MiikaRitokangas/SpedenSpelit/buttons.h

#ifndef BUTTONS_H
#define BUTTONS_H
#include <arduino.h>
#include <avr/io.h>
#include <avr/interrupt.h>

#define BUTTON0_PIN 2
#define BUTTON1_PIN 3
#define BUTTON2_PIN 4
#define BUTTON3_PIN 5
#define BUTTON4_PIN 6

const byte firstPin = 2; // First PinChangeInterrupt on D-bus
const byte lastPin =  5; // Last PinChangeInterrupt on D-bus

/* 
  initButtonsAndButtonInterrupts subroutine is called from Setup() function
  during the initialization of Speden Spelit. This function does the following:
  1) Initializes 4 button pins for the game = Arduino pins 2,3,4,5
  2) Initializes 1 button pin for starting the game = Aruino pin 6
  3) Enables PinChangeInterrupt on D-bus in a way that interrupt
     is generated whenever some of pins 2,3,4,5,6 is connected to LOW state

*/
void initButtonsAndButtonInterrupts(void);


// Intoduce PCINT2_vect Interrupt SeRvice (ISR) function for Pin Change Interrupt.
ISR(PCINT2_vect); 
#endif;
